piecol/CM5_MINIMA_REV2/PICS/img_0349.jpg

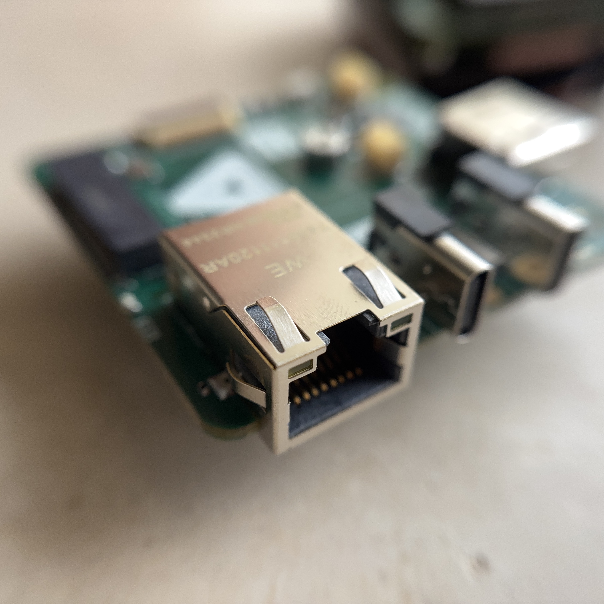
PICS/img_0349.jpg
